Ulf-vom-Mond/ofen_v2/main/type_k_array.h

#pragma once

#include <avr/pgmspace.h>

#define TEMP_STEP 5

// const uint16_t voltages[] PROGMEM = {0, 1, 2, 3, 5, 6, 8, 10, 12, 14, 17, 20, 23, 26, 29, 33, 37, 41, 45, 50, 54, 59, 65, 70, 76, 81, 88, 94, 100, 107, 114, 121, 129, 136, 144, 152, 161, 169, 178, 187, 196, 206, 215, 225, 235, 245, 256, 266, 277, 288, 300, 311, 323, 335, 347, 359, 371, 384, 397, 410, 423, 437, 451, 464, 478, 493, 507, 522, 536, 551, 567, 582, 597, 613, 629, 645, 661, 678, 695, 711, 728, 745, 763, 780, 798, 816, 834, 852, 870, 889, 908, 927, 946, 965, 984, 1004, 1023, 1043, 1063, 1084, 1104, 1125, 1145, 1166, 1187, 1208, 1230, 1251, 1273, 1295, 1317, 1339, 1361, 1384, 1406, 1429, 1452, 1475, 1498, 1522, 1545, 1569, 1593, 1617, 1641, 1665, 1690, 1714, 1739, 1764, 1789, 1814, 1840, 1865, 1891, 1916, 1942, 1968, 1995, 2021, 2047, 2074, 2101, 2128, 2155, 2182, 2209, 2237, 2264, 2292, 2320, 2348, 2376, 2403, 2432, 2461, 2490, 2519, 2547, 2576, 2606, 2635, 2664, 2694, 2724, 2753, 2783, 2813, 2844, 2874, 2904, 2935, 2966, 2996, 3027, 3058, 3090, 3121, 3152, 3184, 3215, 3247, 3279, 3311, 3343, 3375, 3408, 3440, 3472, 3505, 3538, 3571, 3604, 3637, 3670, 3703, 3737, 3770, 3804, 3838, 3871, 3905, 3939, 3973, 4008, 4042, 4076, 4111, 4146, 4180, 4215, 4250, 4285, 4320, 4355, 4391, 4426, 4462, 4497, 4533, 4569, 4604, 4640, 4676, 4713, 4749, 4785, 4821, 4858, 4894, 4931, 4968, 5005, 5041, 5078, 5115, 5153, 5190, 5227, 5264, 5302, 5339, 5377, 5415, 5452, 5490, 5528, 5566, 5604, 5642, 5680, 5719, 5757, 5795, 5834, 5872, 5911, 5950, 5988, 6027, 6066, 6105, 6144, 6183, 6222, 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

// starts at -270 degrees celsius and increments 5 K per field. Voltages are in microvolts and are 6458 microvolts higher than in reality. Takes about 660 Bytes of program memory.
